auomoto/BOSS-specMech/Software/BasicMicro/2022-05-01 Motion Studio Screen General Settings.PNG

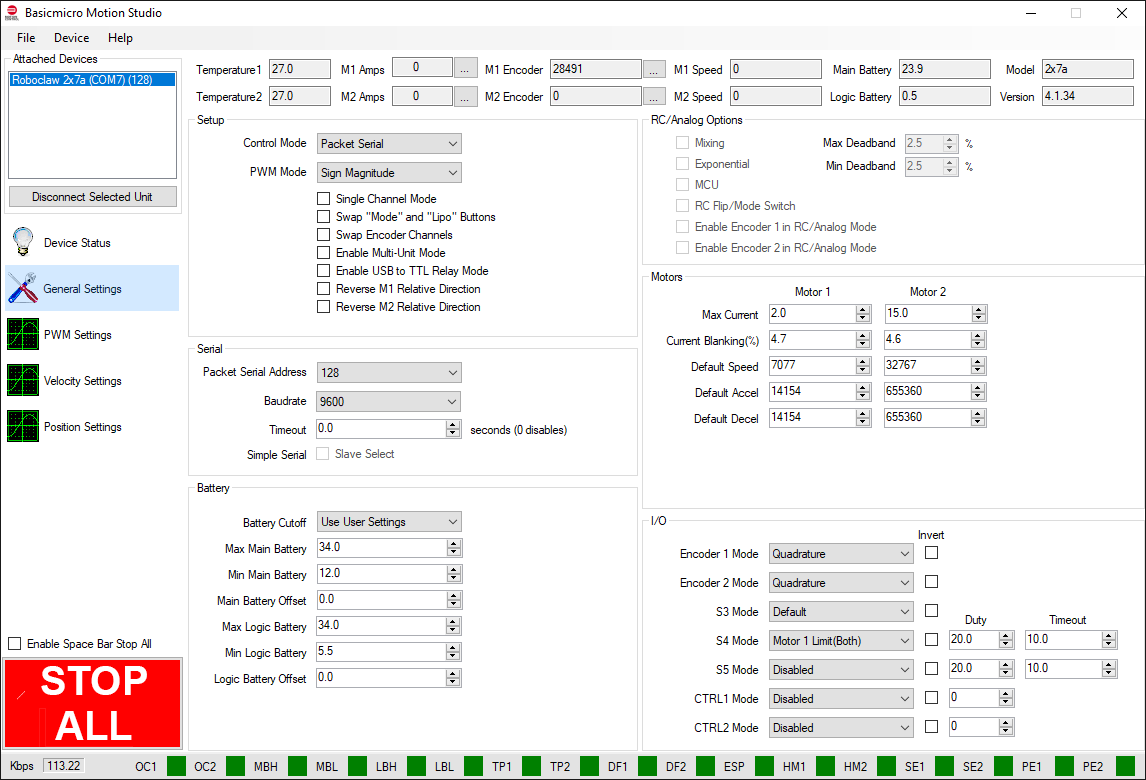
Software/BasicMicro/2022-05-01 Motion Studio Screen General Settings.PNG
