auomoto/BOSS-specMech/Software/Atmel Studio/specMech/roboclaw.c

#include "globals.h"
#include "roboclaw.h"

volatile uint8_t timerSAVEENCODER;
uint8_t timeoutSAVEENCODER, motorDir[3], motorLim[3];
PID pid;

/*------------------------------------------------------------------------------
uint16_t crc16(uint8_t *packet, uint16_t nbytes)

	RoboClaw sends a CRC16 word at the end of data packets and requires a CRC16
	word at the end of commands that send data (not just a command). See page 59
	of the RoboClaw user manual Rev 5.7 (2015) for this routine.

	Inputs:
		packet - array to compute
		nBytes - length of the array

	Returns:
		The CRC16 value, an unsigned 16-bit word
------------------------------------------------------------------------------*/
uint16_t crc16(uint8_t *packet, uint16_t nBytes)
{

	uint8_t bit;
	uint16_t crc = 0;
	int16_t byte;

	for (byte = 0; byte < nBytes; byte++) {
		crc = crc ^ ((uint16_t) packet[byte] << 8);
		for (bit = 0; bit < 8; bit++) {
			if (crc & 0x8000) {
				crc = (crc << 1) ^ 0x1021;
			} else {
				crc = crc << 1;
			}
		}
	}

	return (crc);

}

uint8_t get_FRAM_ENCSAVETIME(char *isotime)
{

	char strbuf[80];
	const char fmt0[] = "get_FRAM_ENCSAVETIME: read_FRAM error";

	if (read_FRAM(FRAMTWIADDR, ENC_SAVETIME, (uint8_t*) isotime, 20) == ERROR) {
		sprintf(strbuf, fmt0);
		printError(ERR_MTR, strbuf);
		return(ERROR);
	}
	isotime[19] = '\0';
	return(NOERROR);

}

/*------------------------------------------------------------------------------
uint8_t get_FRAM_MOTOR_ENCODER(uint8_t controller, uint32_t *encoderValue)

	Retrieves the encoder value stored in FRAM.

	Inputs:
		controller: The controller address: MOTOR_A, MOTOR_B, or MOTOR_C

	Outputs:
		encoderValue: The stored encoder value

	Returns:
		ERROR on FRAM read error
		NOERROR otherwise
------------------------------------------------------------------------------*/
uint8_t get_FRAM_MOTOR_ENCODER(uint8_t controller, int32_t *encoderValue)
{

	char strbuf[80];
	uint8_t tbuf[4];
	uint16_t framaddr;
	const char fmt0[] ="get_FRAM_MOTOR_ENCODER: read_FRAM error for %c";

	switch (controller) {

		case MOTOR_A:
			framaddr = ENCA_FRAMADDR;
			break;

		case MOTOR_B:
			framaddr = ENCB_FRAMADDR;
			break;

		case MOTOR_C:
			framaddr = ENCC_FRAMADDR;
			break;

		default:
			return(ERROR);

	}

	if (read_FRAM(FRAMTWIADDR, framaddr, tbuf, 4) == ERROR) {
		sprintf(strbuf, fmt0, (char) (controller-63));
		printError(ERR_FRAM, strbuf);
		*encoderValue = BADLONG;
		return(ERROR);
	}

	*encoderValue =  (uint32_t) tbuf[0] << 24;
	*encoderValue |= (uint32_t) tbuf[1] << 16;
	*encoderValue |= (uint32_t) tbuf[2] << 8;
	*encoderValue |= (uint32_t) tbuf[3];

	return(NOERROR);

}

/*------------------------------------------------------------------------------
uint8_t get_MOTOR(uint8_t mtraddr, uint8_t cmd, uint8_t* data, uint8_t nbytes)

	Retrieves raw data from the motor controller "mtraddr"

	Inputs:
		mtraddr:	MOTOR_A, MOTOR_B, or MOTOR_C (128, 129, or 130)
		command:	The motor controller packet serial command
		nbytes:		Number of bytes expected from the motor controller,
					not including the two CRC bytes.

	Output:
		data:		Array to receive the data. Undefined if ERROR returned.

	Returns
		ERROR on USART timeout or CRC mismatch
		NOERROR otherwise
------------------------------------------------------------------------------*/
uint8_t get_MOTOR(uint8_t mtraddr, uint8_t cmd, uint8_t* data, uint8_t nbytes)
{

	char strbuf[80];
	uint8_t i, nbytesp2, tbuf[nbytes+2];
	uint16_t crc, crcReceived, crcExpected;
	const char fmt0[] = "get_MOTOR: serial timeout on %c";
	const char fmt1[] = "get_MOTOR: CRC mismatch on %c";

	nbytesp2 = nbytes + 2;
	ser_recv1.nxfrd = 0;			// Set up receive buffer
	ser_recv1.n2xfr = nbytesp2;		// Data plus 2 bytes CRC

	tbuf[0] = mtraddr;				// Motor controller serial address
	tbuf[1] = cmd;					// Motor controller command
	crc = crc16(tbuf, 2);
	tbuf[2] = (crc >> 8) & 0xFF;
	tbuf[3] = crc & 0xFF;

#ifdef VERBOSE
	sprintf(strbuf, " addr=%d cmd=%d crc=0x%04X n2xfr=%d",
		mtraddr, cmd, crc, nbytesp2);
	printLine(strbuf);
#endif

	send_USART1(tbuf, 2);

	USART1_ticks = 0;
	while (ser_recv1.nxfrd < ser_recv1.n2xfr) {
		if (USART1_ticks > 100) {		// Check the number
			sprintf(strbuf, fmt0, (char) (mtraddr-63));
			printError(ERR_MTRREADENC, strbuf);

#ifdef VERBOSE
			break;
#endif
			return(ERROR);
		}
	}

#ifdef VERBOSE
	sprintf(strbuf, " get_MOTOR: USART1_ticks=%d nxfrd=%d", USART1_ticks, ser_recv1.nxfrd);
	printLine(strbuf);
	for (i = 0; i < ser_recv1.nxfrd; i++) {
		sprintf(strbuf, " n=%d %d (0x%02X)", i, ser_recv1.data[i], ser_recv1.data[i]);
		printLine(strbuf);
	}
#endif

	crcReceived = (ser_recv1.data[nbytes] << 8) | ser_recv1.data[nbytes+1];

	for (i = 2; i < nbytesp2; i++) {		// Compute expected crc value
		tbuf[i] = ser_recv1.data[i-2];
	}
	crcExpected = crc16(tbuf, nbytesp2);

	if (crcReceived != crcExpected) {
		sprintf(strbuf, fmt1, (char) (mtraddr-63));
		printError(ERR_MTRENCCRC, strbuf);
		return(ERROR);
	}

	for (i = 0; i < nbytes; i++) {
		data[i] = ser_recv1.data[i];
	}

	return(NOERROR);	

}

/*------------------------------------------------------------------------------
uint8_t get_MOTOR_CURRENT(uint8_t mtraddr, int16_t *current)

	Retrieves motor current in mA from mtraddr

	Inputs:
		mtraddr: MOTOR_A, MOTOR_B, or MOTOR_C (128, 129, or 130)

	Output:
		current: The current in mA

	Returns
		ERROR on USART timeout
		NOERROR otherwise

	This command returns the current for both motor 1 and motor 2. We only
	have a motor 1 so we discard the 2nd value.
------------------------------------------------------------------------------*/
uint8_t get_MOTOR_CURRENT(uint8_t mtraddr, uint16_t *current)
{

	const char fmt0[] = "get_MOTOR_CURRENT: get_MOTOR error on %c";
	char strbuf[80];
	uint8_t data[4];

	if (get_MOTOR(mtraddr, READCURRENT, data, 4) == ERROR) {
		sprintf(strbuf, fmt0, (char) (mtraddr-63));
		printError(ERR_MTR, strbuf);
		*current = BADINT;
		return(ERROR);
	}

	*current = (((uint16_t) data[0] << 8) | (uint16_t) data[1]) * 10;

	return(NOERROR);

}

/*------------------------------------------------------------------------------
uint8_t get_MOTOR_ENCODER(uint8_t mtraddr, int32_t *encoderValue)

	Retrieves the 32-bit encoder value from the controller at mtraddr

	Inputs:
		mtraddr: MOTOR_A, MOTOR_B, or MOTOR_C (128, 129, or 130)

	Output:
		encoderValue: The raw encoder value

	Returns
		ERROR on USART timeout
		NOERROR otherwise

	Also available with this command but not output here:
		status - from page 86 of version 5.7 of the manual:
			Bit0: Counter underflow (1=underflow occurred, clear after reading)
			Bit1: Direction (0=forward, 1-backwards)
			Bit2: Counter overflow (1=overflow occurred, clear after reading)
			Bits 3-7 are "reserved." Bit7 is 1.
------------------------------------------------------------------------------*/
uint8_t get_MOTOR_ENCODER(uint8_t mtraddr, int32_t *encoderValue)
{

	char strbuf[80];
	uint8_t data[5];	// 5 bytes includes status, which is ignored here
	const char fmt0[] = "get_MOTOR_ENCODER: get_MOTOR error on %c";

	if (get_MOTOR(mtraddr, ENCODERCOUNT, data, 5) == ERROR) {
		sprintf(strbuf, fmt0, (char) (mtraddr-63));
		printError(ERR_MTR, strbuf);
		return(ERROR);
	}

	*encoderValue =  (uint32_t) data[0] << 24;
	*encoderValue |= (uint32_t) data[1] << 16;
	*encoderValue |= (uint32_t) data[2] << 8;
	*encoderValue |= (uint32_t) data[3];

#ifdef VERBOSE
	sprintf(strbuf, " encval=%ld", *encoderValue);
	printLine(strbuf);
#endif

	return(NOERROR);

}

/*------------------------------------------------------------------------------
uint8_t get_MOTOR_FLOAT(uint8_t mtraddr, uint8_t cmd, float *value)

	Retrieves a floating point value (the voltage or temperature) from a
	RoboClaw controller.

	Inputs:
		mtraddr:	Controller address (128, 129, 130)
		cmd:		READMAINVOLTAGE (command 24) or
					READTEMPERATURE (command 82)

	Outputs:
		value:		The integer value from the command in increments of tenths of
					a volt or tenths of a degree. The value returned is divided by 10
					to present units of degrees C and volts.

	Returns:
		ERROR on a bad get_MOTOR call
		NOERROR otherwise
------------------------------------------------------------------------------*/
uint8_t get_MOTOR_FLOAT(uint8_t mtraddr, uint8_t cmd, float* value)
{

	char strbuf[80];
	uint8_t data[2];
	const char fmt0[] = "get_MOTOR_FLOAT: get_MOTOR error on %c";

	if (get_MOTOR(mtraddr, cmd, data, 2) == ERROR) {
		sprintf(strbuf, fmt0, (char) (mtraddr-63));
		printError(ERR_MTR, strbuf);
		*value = BADFLOAT;
		return(ERROR);
	}

	*value = ((float) ((data[0] << 8) | data[1])) / 10.0;

	return(NOERROR);

}

uint8_t get_MOTOR_LIMIT(uint8_t mtraddr)
{

	char strbuf[80];
	const char fmt0[] = "get_MOTOR_LIMIT: get_MOTOR_STATUS error on %c";
	uint32_t robostatus;

	if (get_MOTOR_STATUS(mtraddr, &robostatus) == ERROR) {
		sprintf(strbuf, fmt0, (char) (mtraddr - 31));
		printError(ERR_MTR, strbuf);
	}

	if (robostatus & 0x400000) {
		return(YES);
	} else {
		return(NO);
	}

}


/*------------------------------------------------------------------------------
uint8_t get_MOTOR_LIMITS(void)

	Finds the limit switch stored state for every motor.

	Input:
		None

	Output:
		motorLim[n] limit switch states YES, NO, or MTRLIMUNKNOWN

	Returns:
		ERROR on get_MOTOR_STATUS error (quietly)
		NOERROR otherwise

	Note: This does not read the limit switch directly. When the limit switch
		is triggered the switch state is saved but the state is cleared
		immediately after a motor motion in the opposite direction, even
		though the switch itself might still be engaged.
------------------------------------------------------------------------------*/
uint8_t get_MOTOR_LIMITS(void)
{

	uint8_t i, mtraddr;
	uint32_t robostatus;

	for (i = 0; i < 3; i++) {
		motorLim[i] = MTRLIMUNKNOWN;
		mtraddr = i + MOTOR_A;
		if (get_MOTOR_STATUS(mtraddr, &robostatus) != ERROR) {
			if (robostatus & 0x400000) {
				motorLim[i] = YES;
			}
		}
	}

	return(NOERROR);

}

/*------------------------------------------------------------------------------
uint8_t get_MOTOR_MAXCURRENT(uint8_t mtraddr, int32_t *maxCurrent)

	Read the maximum current allowed by the controller.

	Input:
		mtraddr:	MOTOR_A, MOTOR_B, or MOTOR_C (128, 129, 130)

	Output:
		maxCurrent:	The maximum current allowed, in mA

	Returns:
		ERROR on get_MOTOR error
		NOERROR otherwise
------------------------------------------------------------------------------*/
uint8_t get_MOTOR_MAXCURRENT(uint8_t mtraddr, int32_t *maxCurrent)
{

	const char fmt0[] = "get_MOTOR_MAXCURRENT: get_MOTOR error on %c";
	char strbuf[80];
	uint8_t data[8];

	if (get_MOTOR(mtraddr, GETMAXCURRENT, data, 8) == ERROR) {
		sprintf(strbuf, fmt0, (char) (mtraddr-63));
		printError(ERR_MTR, strbuf);
		return(ERROR);
	}

	*maxCurrent =  (uint32_t) data[0] << 24;
	*maxCurrent |= (uint32_t) data[1] << 16;
	*maxCurrent |= (uint32_t) data[2] << 8;
	*maxCurrent |= (uint32_t) data[3];
	*maxCurrent *= 10;	// Convert to mA

	return(NOERROR);

}

/*------------------------------------------------------------------------------
uint8_t get_MOTOR_PID(uint8_t mtraddr, PID *pid)

	Retrieves the PID, maxI, deadZone, minPos, and maxPos from mtraddr

	Inputs:
		mtraddr: The motor controller address(MOTOR_A, MOTOR_B, or MOTOR_C)

	Outputs:
		pid: The stored parameters in the controller

	Returns:
		ERROR on get_MOTOR fail
		NOERROR otherwise
------------------------------------------------------------------------------*/
uint8_t get_MOTOR_PID(uint8_t mtraddr, PID *pid)
{

	const char fmt0[] = "get_MOTOR_PID: get_MOTOR error on %c";
	char strbuf[80];
	uint8_t data[28];
	int32_t p, i, d, maxI, deadZone, minPos, maxPos, qpps;

	if (get_MOTOR(mtraddr, READPID, data, 28) == ERROR) {
		sprintf(strbuf, fmt0, (char) (mtraddr-63));
		printError(ERR_MTR, strbuf);
		return(ERROR);
	}

	p =  (uint32_t) data[0] << 24;
	p |= (uint32_t) data[1] << 16;
	p |= (uint32_t) data[2] << 8;
	p |= (uint32_t) data[3];
	pid->p = (float) p / 1024.0;

	i =  (uint32_t) data[4] << 24;
	i |= (uint32_t) data[5] << 16;
	i |= (uint32_t) data[6] << 8;
	i |= (uint32_t) data[7];
	pid->i = (float) i / 1024.0;

	d =  (uint32_t) data[8] << 24;
	d |= (uint32_t) data[9] << 16;
	d |= (uint32_t) data[10] << 8;
	d |= (uint32_t) data[11];
	pid->d = (float) d / 1024.0;

	maxI =  (uint32_t) data[12] << 24;
	maxI |= (uint32_t) data[13] << 16;
	maxI |= (uint32_t) data[14] << 8;
	maxI |= (uint32_t) data[15];
	pid->maxI = maxI;

	deadZone =  (uint32_t) data[16] << 24;
	deadZone |= (uint32_t) data[17] << 16;
	deadZone |= (uint32_t) data[18] << 8;
	deadZone |= (uint32_t) data[19];
	pid->deadZone = deadZone;

	minPos =  (uint32_t) data[20] << 24;
	minPos |= (uint32_t) data[21] << 16;
	minPos |= (uint32_t) data[22] << 8;
	minPos |= (uint32_t) data[23];
	pid->minPos = minPos;

	maxPos =  (uint32_t) data[24] << 24;
	maxPos |= (uint32_t) data[25] << 16;
	maxPos |= (uint32_t) data[26] << 8;
	maxPos |= (uint32_t) data[27];
	pid->maxPos = maxPos;

	if (get_MOTOR(mtraddr, READQPPS, data, 16) == ERROR) {
		sprintf(strbuf, fmt0, (char) (mtraddr-63));
		printError(ERR_MTR, strbuf);
		return(ERROR);
	}

	qpps = (uint32_t) data[12] << 24;
	qpps |= (uint32_t) data[13] << 16;
	qpps |= (uint32_t) data[14] << 8;
	qpps |= (uint32_t) data[15];
	pid->qpps = qpps;

	return(NOERROR);

}

/*------------------------------------------------------------------------------
uint8_t get_MOTOR_S4MODE(uint8_t mtraddr, uint8_t *mode)

	Retrieve the S4 input pin behavior. The S4 pin is connected to both the
	forward and rearward limit switches. We want to see 0x42 mode, which means
	the S4 pin treats sees a home switch when moving backwards and a limit
	switch when moving forward. When encountering the home switch, the 2x7A
	controller resets the encoder value to 0 (actually, something close).

	Inputs:
		mtraddr:	The controller serial address

	Outputs:
		*mode:		The retrieved mode for the S4 pin (should be 0x72)

	Returns:
		ERROR if the get_MOTOR routine fails
		NOERROR otherwise

	Note: One of the modes, Motor 1 Limit(Both) returns 0x02 when it should
		return 0x32
------------------------------------------------------------------------------*/
uint8_t get_MOTOR_S4MODE(uint8_t mtraddr, uint8_t *mode)
{

	const char fmt0[] = "get_MOTOR_S4: get_MOTOR error on %c";
	char strbuf[80];
	uint8_t data[3];

	if (get_MOTOR(mtraddr, GETS4MODE, data, 3) == ERROR) {
		sprintf(strbuf, fmt0, (char) (mtraddr-63));
		printError(ERR_MTR, strbuf);
		*mode = 0xFF; 
		return(ERROR);
	}

	*mode = data[1];

	return(NOERROR);

}

/*------------------------------------------------------------------------------
uint8_t get_MOTOR_SPEED(uint8_t mtraddr, int32_t *speed)

	Retrieves the motor speed from the controller at mtraddr

	Inputs:
		mtraddr:	MOTOR_A, MOTOR_B, or MOTOR_C (128, 129, or 130)

	Output:
		speed:		The speed in encoder counts/sec. 2-s complement value.

	Returns
		ERROR on USART timeout
		NOERROR otherwise

	Also available with this command but not output here:
		status - from page 86 of version 5.7 of the manual:
			Bit0: Counter underflow (1=underflow occurred, clear after reading)
			Bit1: Direction (0=forward, 1-backwards)
			Bit2: Counter overflow (1=overflow occurred, clear after reading)
			Bits 3-7 are "reserved." Bit7 is 1.
------------------------------------------------------------------------------*/
uint8_t get_MOTOR_SPEED(uint8_t mtraddr, int32_t *speed)
{

	char strbuf[80];
	uint8_t data[5];
	const char fmt0[] = "get_MOTOR_SPEED: get_MOTOR call error on %c";

	if (get_MOTOR(mtraddr, ENCODERSPEED, data, 5) == ERROR) {
		sprintf(strbuf, fmt0, (char) (mtraddr-63));
		printError(ERR_MTR, strbuf);
		return(ERROR);
	}

	*speed =  (uint32_t) data[0] << 24;
	*speed |= (uint32_t) data[1] << 16;
	*speed |= (uint32_t) data[2] << 8;
	*speed |= (uint32_t) data[3];

	return(NOERROR);

}

/*------------------------------------------------------------------------------
uint8_t get_MOTOR_STATUS(uint8_t mtraddr, uint32_t *robostatus)

	Reads the motor controller status. Command 90, see page 73 of the RoboClaw
	User Manual, Revision 5.7. We use this to determine if a limit switch has
	been triggered (the S4 pin is pulled low). The bitmask for S4 is 0x400000.

	Input:
		Motor address (128, 129, or 130).

	Output:
		The 32-bit word in robostatus.

	Returns:
		ERROR if the get_MOTOR command fails.

------------------------------------------------------------------------------*/
uint8_t get_MOTOR_STATUS(uint8_t mtraddr, uint32_t *robostatus)
{
	
	char strbuf[80];
	const char fmt0[] = "get_MOTOR_STATUS: get_MOTOR error %c";
	uint8_t data[4];

	if (get_MOTOR(mtraddr, ROBOSTATUS, data, 4) == ERROR) {
		sprintf(strbuf, fmt0, (char) mtraddr-63);
		printError(ERR_MTR, strbuf);
		return(ERROR);
	}

	*robostatus =  (uint32_t) data[0] << 24;
	*robostatus |= (uint32_t) data[1] << 16;
	*robostatus |= (uint32_t) data[2] << 8;
	*robostatus |= (uint32_t) data[3];

	return(NOERROR);

}

/*------------------------------------------------------------------------------
uint8_t init_MOTORS(void)
	Reads the last-saved encoder values from FRAM and loads them into the three
	controllers.

	Inputs: None

	Outputs: None

	Returns
		ERROR if put_MOTOR_ENCODER fails
		NOERROR otherwise

ADD ERROR CHECKS?
------------------------------------------------------------------------------*/
uint8_t init_MOTORS(void)
{

	uint8_t i, mtraddr;
	int32_t encoderValue;

	_delay_ms(100);		// Wait to boot up
	timerSAVEENCODER = 0;
	timeoutSAVEENCODER = SAVEENCODERPERIOD;

	for (i = 0; i < NMOTORS; i++) {
		motorDir[i] = MTRDIRUNKNOWN;
		motorLim[i] = MTRLIMUNKNOWN;
		mtraddr = i + MOTOR_A;
		get_FRAM_MOTOR_ENCODER(mtraddr, &encoderValue);
		put_MOTOR_ENCODER(mtraddr, encoderValue);
	}

	return(NOERROR);

}

/*------------------------------------------------------------------------------
uint8_t motorMoving(uint8_t mtraddr)

	Checks encoder speed to see if the motor is moving

	Input:
		mtraddr: The controller address

	Output:
		None

	Returns:
		YES if the motor is moving
		NO if it isn't
------------------------------------------------------------------------------*/
uint8_t motorMoving(uint8_t mtraddr)
{

	const char fmt0[] = "motorMoving: get_MOTOR_SPEED error on %c";
	char strbuf[80];
	int32_t encoderSpeed;

	encoderSpeed = 0;
	if (get_MOTOR_SPEED(mtraddr, &encoderSpeed) == ERROR) {
		sprintf(strbuf, fmt0, (char) (mtraddr-63));
		printError(ERR_MTR, strbuf);
		return(ERROR);
	}

	if (encoderSpeed != 0) {
		return(YES);
	} else {
		return(NO);
	}

}

/*------------------------------------------------------------------------------
uint8_t motorsMoving(void)
	Returns YES if any motors are moving. Emits an error message if a
	controller does not respond, but does not return "ERROR"
------------------------------------------------------------------------------*/
uint8_t motorsMoving(void)
{

	const char fmt1[] = "motorsMoving: get_MOTOR_SPEED error on %c";
	char strbuf[80];
	uint8_t i, mtraddr, nmoving;
	int32_t encoderSpeed;

	encoderSpeed = 0;
	nmoving = 0;

	for (i = 0; i < NMOTORS; i++) {
		mtraddr = i + MOTOR_A;
		if (get_MOTOR_SPEED(mtraddr, &encoderSpeed) == ERROR) {
			sprintf(strbuf, fmt1, (char) (mtraddr-63));
			printError(ERR_MTR, strbuf);
			continue;
		}
		if (encoderSpeed != 0) {
			nmoving++;
		}
	}

	if (nmoving) {
		return(YES);
	} else {
		return(NO);
	}

}

/*------------------------------------------------------------------------------
uint8_t move_MOTOR(uint8_t mtraddr, int32_t newPosition)
	Move to newPosition (encoder units).

	Input:
		mtraddr:		MOTOR_A, MOTOR_B, or MOTOR_C
		newPosition:	The target encoder value

	Returns:
		ERROR if an unknown motor designator
		NOERROR otherwise
------------------------------------------------------------------------------*/
uint8_t move_MOTOR(uint8_t mtraddr, int32_t newPosition)
{

	const char fmt1[] = "move_MOTOR: put_MOTOR error on %c";
	char strbuf[80];
	uint8_t buffer, data[17], nbytes, mtrIndex;
	uint32_t acceleration, deceleration, speed;
	int32_t oldPosition;

	nbytes = 17;
	buffer = 1;
	acceleration = ACCELERATION;	// See roboclaw.h
	deceleration = DECELERATION;
	speed = SPEED;
	mtrIndex = mtraddr - MOTOR_A;

	get_MOTOR_ENCODER(mtraddr, &oldPosition);

	if (newPosition == oldPosition) {
		return(NOERROR);
	}

	data[0] = (acceleration >> 24) & 0XFF;
	data[1] = (acceleration >> 16) & 0xFF;
	data[2] = (acceleration >> 8) & 0xFF;
	data[3] = (acceleration) & 0xFF;
	data[4] = (speed >> 24) & 0xFF;
	data[5] = (speed >> 16) & 0xFF;
	data[6] = (speed >> 8) & 0xFF;
	data[7] = (speed) & 0xFF;
	data[8] = (deceleration >> 24) & 0xFF;
	data[9] = (deceleration >> 16) & 0xFF;
	data[10] = (deceleration >> 8) & 0xFF;
	data[11] = (deceleration) & 0xFF;
	data[12] = (newPosition >> 24) & 0xFF;
	data[13] = (newPosition >> 16) & 0xFF;
	data[14] = (newPosition >> 8) & 0xFF;
	data[15] = (newPosition) & 0xFF;
	data[16] = buffer;

#ifdef VERBOSE
	sprintf(strbuf, " move_MOTOR to newpos=%ld", newPosition);
	printLine(strbuf);
#endif

	if (newPosition > oldPosition) {
		motorDir[mtrIndex] = MTRDIRPOSITIVE;
	} else if (newPosition < oldPosition) {
		motorDir[mtrIndex] = MTRDIRNEGATIVE;
	}

	if (put_MOTOR(mtraddr, DRIVETO, data, nbytes) == ERROR) {
		motorDir[mtrIndex] = MTRDIRUNKNOWN;
		sprintf(strbuf, fmt1, (char) (mtraddr-63));
		printError(ERR_MTR, strbuf);
		return(ERROR);
	}

	return(NOERROR);

}

/*------------------------------------------------------------------------------
uint8_t move_MOTOR_CMD(uint8_t cstack)
	Interprets the m command and calls for the move

	Input:
		cstack: command stack position

	Returns:
		ERROR if an unknown motor designator (not A, B, C, or a, b, c) is read
		NOERROR otherwise
------------------------------------------------------------------------------*/
uint8_t move_MOTOR_CMD(uint8_t cstack)
{

	char strbuf[80];
	uint8_t motor, controller;
	int32_t newPosition, currentPosition, deltaPos;
	const char fmt0[] = "move_MOTOR_CMD: get_MOTOR_ENCODER error";
	const char fmt1[] = "move_MOTOR_CMD: unknown motor";
	const char fmt2[] = "move_MOTOR_CMD: move_MOTOR error";
	const char fmt3[] = "move_MOTOR_CMD: move_MOTORS_PISTON error";

	if (pcmd[cstack].cvalue[0] == '\0') {	// Don't do anything on null distance
		return(NOERROR);
	}

	motor = pcmd[cstack].cobject;

	switch(motor) {

		case 'A':			// Move absolute
		case 'B':
		case 'C':
			controller = motor + 63;
			if (get_MOTOR_ENCODER(controller, &currentPosition) == ERROR) {
				sprintf(strbuf, fmt0);
				printError(ERR_MTR_ENC_VAL, strbuf);
				return(ERROR);
			}
			newPosition = (atol(pcmd[cstack].cvalue) * ENC_COUNTS_PER_MICRON);
			break;

		case 'a':			// Move relative
		case 'b':
		case 'c':
			controller = motor + 31;
			if (get_MOTOR_ENCODER(controller, &currentPosition) == ERROR) {
				sprintf(strbuf, fmt0);
				printError(ERR_MTR_ENC_VAL, strbuf);
				return(ERROR);
			}
			newPosition = currentPosition + (atol(pcmd[cstack].cvalue) * ENC_COUNTS_PER_MICRON);
			break;

		case 'd':
			deltaPos = (atol(pcmd[cstack].cvalue) * ENC_COUNTS_PER_MICRON);
			if (move_MOTORS_PISTON(deltaPos) == ERROR) {
				sprintf(strbuf, fmt3);
				printError(ERR_MTR, strbuf);
				return(ERROR);
			}
			return(NOERROR);

		default:
			sprintf(strbuf, fmt1);
			printError(ERR_MTR, strbuf);
			return(ERROR);
			break;	
	}

	motorDir[controller - MOTOR_A] = MTRDIRUNKNOWN;

	if (move_MOTOR(controller, newPosition) == ERROR) {
		sprintf(strbuf, fmt2);
		printError(ERR_MTR, strbuf);
		return(ERROR);
	}

	if (newPosition < currentPosition) {
		motorDir[controller - MOTOR_A] = MTRDIRNEGATIVE;
	} else if (newPosition > currentPosition) {
		motorDir[controller - MOTOR_A] = MTRDIRPOSITIVE;
	}

	return(NOERROR);

}

uint8_t move_MOTOR_HOME(void)
{

	const char fmt0[] = "move_MOTOR_HOME: timeout";
	const char fmt1[] = "move_MOTOR_HOME: get_MOTOR_ENCODER error on %c";
	const char fmt2[] = "move_MOTOR_HOME: move_MOTOR error on %c";
	const char fmt3[] = "move_MOTOR_HOME: motors didn't align";
	char strbuf[80];
	uint8_t i, mtraddr;
	int32_t curPos[3], avgPos;

	avgPos = 0;

	for (i = 0; i < 1; i++) {
//	for (i = 0; i < 3; i++) {
		mtraddr = i + MOTOR_A;
		if (get_MOTOR_ENCODER(mtraddr, &curPos[i]) == ERROR) {
			sprintf(strbuf, fmt1, (char) (mtraddr-63));
			printError(ERR_MTR, strbuf);
			return(ERROR);
		}
		avgPos += curPos[i];
	}
	avgPos /= 3;

#ifdef VERBOSE
	sprintf(strbuf, " avgPos = %ld", avgPos/ENC_COUNTS_PER_MICRON);
	printLine(strbuf);
#endif

	for (mtraddr = MOTOR_A; mtraddr <= MOTOR_A; mtraddr++) {
//	for (mtraddr = MOTOR_A; mtraddr <= MOTOR_C; mtraddr++) {
		if (move_MOTOR(mtraddr, avgPos) == ERROR) {
			sprintf(strbuf, fmt2, (char) (mtraddr-63));
			printError(ERR_MTR, strbuf);
			return(ERROR);
		}
	}

	_delay_ms(250);		// give motors a chance to start up

// BREAK UP THIS ROUTINE INTO PIECES CONTROLLED FROM MAIN

	i = 0;
	while (motorsMoving()) {
		if (i > 20) {				// get this number right later
			sprintf(strbuf, fmt0);
			printError(ERR_MTR, strbuf);
			return(ERROR);
		}
		i++;
		_delay_ms(1000);
	}

#ifdef VERBOSE
	sprintf(strbuf, " stopped after %d", i);
	printLine(strbuf);
#endif

	for (i = 0; i < 1; i++) {
//	for (i = 0; i < 4; i++) {
		mtraddr = i + MOTOR_A;
		if (get_MOTOR_ENCODER(mtraddr, &curPos[i]) == ERROR) {
			sprintf(strbuf, fmt1, mtraddr-63);
			printError(ERR_MTR, strbuf);
			return(ERROR);
		}
	}

	// Check that all motors are at the same position
	if (abs( (int)(curPos[0] - curPos[1]) ) > ENC_COUNTS_PER_MICRON) {
		sprintf(strbuf, fmt3);
		printError(ERR_MTR, strbuf);
		return(ERROR);
	}
	if (abs( (int)(curPos[0] - curPos[2]) ) > ENC_COUNTS_PER_MICRON) {
		sprintf(strbuf, fmt3);
		printError(ERR_MTR, strbuf);
		return(ERROR);
	}
	// now piston the motors to somewhere close (200 um in this case)
	for (mtraddr = MOTOR_A; mtraddr <= MOTOR_A; mtraddr++) {
//	for (mtraddr = MOTOR_A; mtraddr <= MOTOR_C; mtraddr++) {
		if (move_MOTOR(mtraddr, (int32_t) (200L * ENC_COUNTS_PER_MICRON)) == ERROR) {
			sprintf(strbuf, fmt2, (char) (mtraddr-63));
			printError(ERR_MTR, strbuf);
			return(ERROR);
		}
	}


/*---------

	// and back into the switch
	for (mtraddr = MOTOR_A; mtraddr <= MOTOR_A; mtraddr++) {
//	for (mtraddr = MOTOR_A; mtraddr <= MOTOR_C; mtraddr++) {
		if (move_MOTOR(mtraddr, -100) == ERROR) {
			sprintf(strbuf, fmt2, (char) (mtraddr-63));
			printError(ERR_MTR, strbuf);
			return(ERROR);
		}
	}

	for (mtraddr = MOTOR_A; mtraddr <= MOTOR_A; mtraddr++) {
//	for (mtraddr = MOTOR_A; mtraddr <= MOTOR_C; mtraddr++) {
		if (put_MOTOR_ENCODER(mtraddr, 0UL) == ERROR) {
			sprintf(strbuf, fmt4, (char) (mtraddr-63));
			printError(ERR_MTR, strbuf);
			return(ERROR);
		}
	}

-------------*/

	return(NOERROR);

}

uint8_t move_MOTORS_PISTON(int32_t deltaValue)
{

	char strbuf[80];
	uint8_t i, mtraddr;
	int32_t curPos[3], newPos[3];
	const char fmt0[] = "move_MOTORS_PISTON: get_MOTOR_ENCODER error on %c";
	const char fmt1[] = "move_MOTORS_PISTON: move_MOTOR error on %c";

	for (i = 0; i < NMOTORS; i++) {
		mtraddr = i + MOTOR_A;
		if (get_MOTOR_ENCODER(mtraddr, &curPos[i]) == ERROR) {
			sprintf(strbuf, fmt0, mtraddr-63);
			printError(ERR_MTR, strbuf);
			return(ERROR);
		}
		newPos[i] = curPos[i] + deltaValue;
	}

	for (i = 0; i < NMOTORS; i++) {
		mtraddr = i + MOTOR_A;
		if (move_MOTOR(mtraddr, newPos[i]) == ERROR) {
			sprintf(strbuf, fmt1, mtraddr-63);
			printError(ERR_MTR, strbuf);
			return(ERROR);
		}
		motorDir[i] = MTRDIRUNKNOWN;
		if (newPos[i] > curPos[i]) {
			motorDir[i] = MTRDIRPOSITIVE;
		} else if (newPos[i] < curPos[i]) {
			motorDir[i] = MTRDIRNEGATIVE;
		}
	}

	return(NOERROR);

}

/*------------------------------------------------------------------------------
uint8_t put_FRAM_ENCODERS(void)

	Store the encoder values in FRAM.

	Inputs:
		None

	Outputs:
		None

	Returns:
		ERROR on get_MOTOREncoder or write_FRAM failure
		NOERROR otherwise

	Note:
		This routine is called asynchronously and should't emit error
		messages.
------------------------------------------------------------------------------*/
uint8_t put_FRAM_ENCODERS(void)
{

	char isotime[20];
	uint8_t i, tbuf[4], mtraddr;
	uint16_t memaddr[3] = {ENCA_FRAMADDR, ENCB_FRAMADDR, ENCC_FRAMADDR};
	int32_t encoderValue;

	for (i = 0; i < NMOTORS; i++) {
		mtraddr = i + MOTOR_A;
		if (get_MOTOR_ENCODER(mtraddr, &encoderValue) == ERROR) {
			return(ERROR);
		}
		tbuf[0] = (encoderValue >> 24) & 0xFF;
		tbuf[1] = (encoderValue >> 16) & 0xFF;
		tbuf[2] = (encoderValue >> 8) & 0xFF;
		tbuf[3] = encoderValue & 0xFF;
		if (write_FRAM(FRAMTWIADDR, memaddr[i], tbuf, 4) == ERROR) {
			return(ERROR);
		}
	}

	get_time(isotime);
	write_FRAM(FRAMTWIADDR, ENC_SAVETIME, (uint8_t*) isotime, 20);

	return(NOERROR);

}

/*------------------------------------------------------------------------------
uint8_t put_MOTOR(uint8_t mtraddr, uint8_t cmd, uint8_t* data, uint8_t nbytes)
	Sends a command to a motor controller. This routine copies data to temporary
	array and adds the two CRC bytes before sending the temporary array to the
	controller.

	Inputs:
		mtraddr:	Motor controller serial address
		cmd:		Motor controller command
		data:		Array containing data to send.
		nbytes:		Number of bytes to send (not including the 2 CRC bytes)

	Outputs:
		Nothing

	Returns:
		ERROR:		If a serial timeout or bad acknowledge is detected
		NOERROR:	Otherwise
------------------------------------------------------------------------------*/
uint8_t put_MOTOR(uint8_t mtraddr, uint8_t cmd, uint8_t* data, uint8_t nbytes)
{

	const char fmt1[] = "put_MOTOR: serial timeout on %c";
	const char fmt2[] = "put_MOTOR: bad ACK on %c, ack=0x%02x";
	char strbuf[80];
	uint8_t i, tbuf[nbytes+4];
	uint16_t crc;

	ser_recv1.nxfrd = 0;				// Set up reply
	ser_recv1.n2xfr = 1;				// Receive only the 0xFF ACK

	tbuf[0] = mtraddr;
	tbuf[1] = cmd;
	for (i = 0; i < nbytes; i++) {
		tbuf[i+2] = data[i];
	}
	crc = crc16(tbuf, nbytes+2);
	tbuf[nbytes+2] = (crc >> 8) & 0xFF;
	tbuf[nbytes+3] = crc & 0xFF;

	send_USART1(tbuf, nbytes+4);		// Send the command

	USART1_ticks = 0;
	while (ser_recv1.nxfrd < ser_recv1.n2xfr) {
		if (USART1_ticks > 100) {
			sprintf(strbuf, fmt1, (char) (mtraddr-63));
			printError(ERR_MTR, strbuf);
			return(ERROR);
		} else {
			asm("nop");
		}
	}

#ifdef VERBOSE
	sprintf(strbuf, " put_MOTOR USART1_ticks=%d", USART1_ticks);
	printLine(strbuf);
#endif

	if (ser_recv1.data[0] != 0xFF) {	// Bad ack
		sprintf(strbuf, fmt2, (char) (mtraddr-31), ser_recv1.data[0]);
		printError(ERR_MTR, strbuf);
		return(ERROR);
	}

	return(NOERROR);
	
}

/*------------------------------------------------------------------------------
uint8_t put_MOTOR_ENCODER(uint8_t mtraddr, int32_t encoderValue)
	Writes a new encoder value to the selected controller.

	Inputs:
		mtraddr:		Motor controller serial address
		encoderValue:	The new encoder value

	Outputs:
		Nothing

	Returns:
		ERROR:		If put_MOTOR returns an error
		NOERROR:	Otherwise
------------------------------------------------------------------------------*/
uint8_t put_MOTOR_ENCODER(uint8_t mtraddr, int32_t encoderValue)
{

	const char fmt1[] = "put_MOTOR_ENCODER: put_MOTOR error on %c";
	char strbuf[80];
	uint8_t data[4];

	data[0] = (encoderValue >> 24) & 0xFF;
	data[1] = (encoderValue >> 16) & 0xFF;
	data[2] = (encoderValue >> 8) & 0xFF;
	data[3] = encoderValue & 0xFF;

	if (put_MOTOR(mtraddr, PUTENCODER, data, 4) == ERROR) {
		sprintf(strbuf, fmt1, (char) (mtraddr-63));
		printError(ERR_MTR, strbuf);
		return(ERROR);
	}

	return(NOERROR);

}

/*------------------------------------------------------------------------------
uint8_t put_MOTOR_MAXCURRENT(uint8_t mtraddr, int32_t maxCurrent)
	Writes the maximum current value to the selected controller. This works even
	though the Basic Micro GUI doesn't reflect the change. Reading the device on
	the GUI also doesn't update the number. Writing the settings from the GUI
	*will* write the values to the controller EPROM.

	Inputs:
		mtraddr:		Motor controller serial address
		maxCurrent:		The maximum current value im mA

	Outputs:
		Nothing

	Returns:
		ERROR:			If put_MOTOR returns an error
		NOERROR:		Otherwise
------------------------------------------------------------------------------*/
/*
uint8_t put_MOTOR_MAXCURRENT(uint8_t mtraddr, int32_t maxCurrent)
{

	const char fmt1[] = "put_MOTOR_MAXCURRENT: put_MOTOR error on %c";
	char strbuf[80];
	uint8_t data[8];

	maxCurrent /= 10;			// convert to 10 mA units
	data[0] = (maxCurrent >> 24) & 0xFF;
	data[1] = (maxCurrent >> 16) & 0xFF;
	data[2] = (maxCurrent >> 8) & 0xFF;
	data[3] = maxCurrent & 0xFF;
	data[4] = data[5] = data[6] = data[7] = 0;
	if (put_MOTOR(mtraddr, PUTMAXCURRENT, data, 8) == ERROR) {
		sprintf(strbuf, fmt1, (char) (mtraddr-63));
		printError(ERR_MTR, strbuf);
		return(ERROR);
	}
	return(NOERROR);
}
*/

/*------------------------------------------------------------------------------
uint8_t put_MOTOR_PID(uint8_t mtraddr, PID pid)
	Writes new PID parameters to the selected controller. Besides P, I, and D,
	the PID structure also contains the maximum integral windup (maxI), deadZone,
	and the minimum and maximum allowable encoder values (minPos and maxPos).

	Inputs:
		mtraddr:	Motor controller serial address
		PID:		The new PID values

	Outputs:
		Nothing

	Returns:
		ERROR:		If put_MOTOR returns an error
		NOERROR:	Otherwise
------------------------------------------------------------------------------*/

uint8_t put_MOTOR_PID(uint8_t mtraddr, PID pid)
{

	const char fmt1[] = "put_MOTOR_PID: put_MOTOR error pid on %c";
	const char fmt2[] = "put_MOTOR_PID: put_MOTOR error qpps on %c";
	char strbuf[80];
	uint8_t data[28];
	int32_t p, i, d;

	p = (int32_t) (pid.p * 1024.0);
	i = (int32_t) (pid.i * 1024.0);
	d = (int32_t) (pid.d * 1024.0);

	data[0] = (d >> 24) & 0xFF;
	data[1] = (d >> 16) & 0xFF;
	data[2] = (d >> 8) & 0xFF;
	data[3] = d & 0xFF;
	data[4] = (p >> 24) & 0xFF;
	data[5] = (p >> 16) & 0xFF;
	data[6] = (p >> 8) & 0xFF;
	data[7] = p & 0xFF;
	data[8] = (i >> 24) & 0xFF;
	data[9] = (i >> 16) & 0xFF;
	data[10] = (i >> 8) & 0xFF;
	data[11] = i & 0xFF;
	data[12] = (pid.maxI >> 24) & 0xFF;
	data[13] = (pid.maxI >> 16) & 0xFF;
	data[14] = (pid.maxI >> 8) & 0xFF;
	data[15] = pid.maxI & 0xFF;
	data[16] = (pid.deadZone >> 24) & 0xFF;
	data[17] = (pid.deadZone >> 16) & 0xFF;
	data[18] = (pid.deadZone >> 8) & 0xFF;
	data[19] = pid.deadZone & 0xFF;
	data[20] = (pid.minPos >> 24) & 0xFF;
	data[21] = (pid.minPos >> 16) & 0xFF;
	data[22] = (pid.minPos >> 8) & 0xFF;
	data[23] = pid.minPos & 0xFF;
	data[24] = (pid.maxPos >> 24) & 0xFF;
	data[25] = (pid.maxPos >> 16) & 0xFF;
	data[26] = (pid.maxPos >> 8) & 0xFF;
	data[27] = pid.maxPos & 0xFF;

	if (put_MOTOR(mtraddr, SETPID, data, 28) == ERROR) {
		sprintf(strbuf, fmt1, (char) (mtraddr-63));
		printError(ERR_MTR, strbuf);
		return(ERROR);
	}

	data[0] = data[1] = data[2] = data[3] = 0;
	data[4] = data[5] = data[6] = data[7] = 0;
	data[8] = data[9] = data[10] = data[11] = 0;
	data[12] = (pid.qpps >> 24) & 0xFF;
	data[13] = (pid.qpps >> 16) & 0xFF;
	data[14] = (pid.qpps >> 8) & 0xFF;
	data[15] = pid.qpps & 0xFF;

	if (put_MOTOR(mtraddr, SETQPPS, data, 16) == ERROR) {
		sprintf(strbuf, fmt2, (char) (mtraddr-63));
		printError(ERR_MTR, strbuf);
		return(ERROR);
	}

	return(NOERROR);
}


/*------------------------------------------------------------------------------
uint8_t put_MOTOR_S4MODE(uint8_t mtraddr)
	Writes the S4 input pin behavior. The S4 pin is connected to both the
	forward and rearward limit switches. We write 0x72, which means the S4 pin
	treats one switch as the home position and the other as a limit.

	Inputs:
		mtraddr:	The controller serial address

	Outputs:
		None

	Returns:
		ERROR if the put_MOTOR routine fails
		NOERROR otherwise
------------------------------------------------------------------------------*/
/*
uint8_t put_MOTOR_S4MODE(uint8_t mtraddr, uint8_t s4mode)
{

	char strbuf[80];
	uint8_t data[3];
	const char fmt0[] = "put_MOTOR_S4MODE: put_MOTOR error on %c";

	data[0] = 0x00;
	data[1] = s4mode;
	data[2] = 0x00;

	if (put_MOTOR(mtraddr, SETS4MODE, data, 3) == ERROR) {
		sprintf(strbuf, fmt0, (char) (mtraddr-63));
		printError(ERR_MTR, strbuf);
		return(ERROR);
	}

	return(NOERROR);

}
*/
/*
uint8_t set_MOTOR_PARAMS(void)
{

	char strbuf[80];
	uint8_t mtraddr;
	PID pid;
	const char fmt0[] = "set_MOTOR_PARAMS: put_MOTOR_MAXCURRENT error on %c";
	const char fmt1[] = "set_MOTOR_PARAMS: put_MOTOR_PID error on %c";
	const char fmt2[] = "set_MOTOR_PARAMS: put_MOTOR_S4MODE error on %c";

	pid.p = PID_P;
	pid.i = PID_I;
	pid.d = PID_D;
	pid.maxI = PID_MAXI;
	pid.deadZone = PID_DEADZONE;
	pid.minPos = PID_MINPOS;
	pid.maxPos = PID_MAXPOS;
	pid.qpps = PID_QPPS;

	for (mtraddr = MOTOR_A; mtraddr <= MOTOR_C; mtraddr++) {
		_delay_ms(12);
		if (put_MOTOR_MAXCURRENT(mtraddr, MAXCURRENT) == ERROR) {
			sprintf(strbuf, fmt0, (char) (mtraddr-63));
			printError(ERR_MTR, strbuf);
			return(ERROR);
		}
		_delay_ms(12);
		if (put_MOTOR_PID(mtraddr, pid) == ERROR) {
			sprintf(strbuf, fmt1, (char) (mtraddr-63));
			printError(ERR_MTR, strbuf);
			return(ERROR);
		}
		_delay_ms(12);
		if (put_MOTOR_S4MODE(mtraddr, S4MODE) == ERROR) {
			sprintf(strbuf, fmt2, (char) (mtraddr-63));
			printError(ERR_MTR, strbuf);
			return(ERROR);
		}
	}

	return(NOERROR);

}
*/
/*------------------------------------------------------------------------------
uint8_t stop_MOTOR(uint8_t mtraddr)
	Immediately stop a motor by sending a command 0.

	Inputs:
		mtraddr - Motor controller address (MOTOR_A, MOTOR_B, MOTOR_C)

	Outputs:
		None

	Returns:
		ERROR if the put_MOTOR command fails
------------------------------------------------------------------------------*/
/*
uint8_t stop_MOTOR(uint8_t mtraddr)
{

	char strbuf[80];
	uint8_t tbuf[1];
	const char fmt[] = "stop_MOTOR: put_MOTOR error on %c";

	tbuf[0] = 0;
	if (put_MOTOR(mtraddr, STOP, tbuf, 1) == ERROR) {
		sprintf(strbuf, fmt, (char) (mtraddr-63));
		printError(ERR_MTR, strbuf);
		return(ERROR);
	}

	return(NOERROR);

}
*/
/*------------------------------------------------------------------------------
uint8_t stop_MOTORS(void)
	Immediately stops all motors

	Inputs:
		None

	Outputs:
		None

	Returns:
		ERROR if the stop_MOTOR command fails
------------------------------------------------------------------------------*/
/*
uint8_t stop_MOTORS(void)
{

	char strbuf[80];
	uint8_t i, data[9], mtraddr, errflag;
	const char fmt[] = "stop_MOTORS: put_MOTOR error on %c";

	errflag = 0;
	for (i = 0; i < 8; i++) {
		data[i] = 0;
	}
	data[8] = 1;		// Buffer flag
	for (i = 0; i < NMOTORS; i++) {
		mtraddr = i + MOTOR_A;
		if (put_MOTOR(mtraddr, STOP, data, 9) == ERROR) {
			sprintf(strbuf, fmt, (char) (mtraddr - 63));
			printError(ERR_MTR, strbuf);
			errflag++;
		}
	}

	if (errflag) {
		return(ERROR);
	} else {
		return(NOERROR);
	}

}
*/

/*------------------------------------------------------------------------------
uint8_t unstick_MOTOR_LIMIT(uint8_t cstack)
	Recover from a limit switch hit

	Input:
		cstack

	Output:
		None

	Returns:
		ERROR
		NOERROR
------------------------------------------------------------------------------*/
uint8_t unstick_MOTOR_LIMIT(uint8_t cstack)
{

	char strbuf[80];
	uint8_t i, mtraddr, mtrIndex, direction, stuck;
	int32_t encodervalue, encoderspeed, newPosition;

	mtraddr = pcmd[cstack].cobject + 31;	// 128, 129, or 130
	mtrIndex = mtraddr - MOTOR_A;
	direction = motorDir[mtrIndex];		// Save the most recent command direction

//sprintf(strbuf, "mtraddr = %d, mtrIndex = %d, direction = %d", mtraddr, mtrIndex, direction);
//printLine(strbuf);

	if (get_MOTOR_LIMIT(mtraddr) == NO) {
		sprintf(strbuf, "motor %c not stuck", mtraddr - 31);
		printError(ERR_MTR, strbuf);
		return(NOERROR);
	}

	stuck = YES;
	get_MOTOR_ENCODER(mtraddr, &encodervalue);

//sprintf(strbuf, "current position = %ld", encodervalue);
//printLine(strbuf);

	for (i = 0; i < 3; i++) {

		// Try the opposite direction first
		if (direction == MTRDIRNEGATIVE) {
			newPosition = encodervalue + 2 * ENC_COUNTS_PER_MICRON;
		} else {
			newPosition = encodervalue - 2 * ENC_COUNTS_PER_MICRON;			
		}

//sprintf(strbuf, "moving to %ld", newPosition);
//printLine(strbuf);

		move_MOTOR(mtraddr, newPosition);
		get_MOTOR_SPEED(mtraddr, &encoderspeed);
		while (encoderspeed) {
			get_MOTOR_SPEED(mtraddr, &encoderspeed);
//sprintf(strbuf, "encoderspeed = %ld", encoderspeed);
//printLine(strbuf);

		}
//		_delay_ms(3000);

		if (get_MOTOR_LIMIT(mtraddr) == NO) {
//sprintf(strbuf, "unstuck at i=%d, opposite direction", i);
//printLine(strbuf);
			stuck = NO;
			break;
		}

		// Try the same direction
		if (direction == MTRDIRNEGATIVE) {
			newPosition = encodervalue - 2 * ENC_COUNTS_PER_MICRON;
		} else {
			newPosition = encodervalue + 2 * ENC_COUNTS_PER_MICRON;
		}
		move_MOTOR(mtraddr, newPosition);
		get_MOTOR_SPEED(mtraddr, &encoderspeed);
		while (encoderspeed) {
			get_MOTOR_SPEED(mtraddr, &encoderspeed);
//sprintf(strbuf, "encoderspeed = %ld", encoderspeed);
//printLine(strbuf);
		}
//		_delay_ms(2000);

		if (get_MOTOR_LIMIT(mtraddr) == NO) {
//sprintf(strbuf, "unstuck at i=%d, same direction", i);
//printLine(strbuf);
			stuck = NO;
			break;
		}
	}
	if (stuck == YES) {		// Tried 3 times and failed
//sprintf(strbuf, "tried 3 times and failed");
//printLine(strbuf);
		return(ERROR);
	}

	// Move 200 um away
	get_MOTOR_ENCODER(mtraddr, &encodervalue);
	if (direction == MTRDIRNEGATIVE) {
		newPosition = encodervalue + 200L * ENC_COUNTS_PER_MICRON;
	} else if (direction == MTRDIRPOSITIVE) {
		newPosition = encodervalue - 200L * ENC_COUNTS_PER_MICRON;
	} 
//sprintf(strbuf, "encodervalue = %ld, newPosition = %ld", encodervalue, newPosition);
//printLine(strbuf);
	move_MOTOR(mtraddr, newPosition);
	return(NOERROR);

}

/*------------------------------------------------------------------------------
void zero_MOTOR_CMD(uint8_t cstack)
	Loads 0 into a motor encoder

	Inputs:
		Command line

	Outputs:
		None
------------------------------------------------------------------------------*/
void zero_MOTOR_CMD(uint8_t cstack)
{

	char strbuf[80];
	const char fmt0[] = "zero_MOTOR_CMD: failed put_MOTOR_ENCODER on %c";
	const char fmt1[] = "zero_MOTOR_CMD: not a motor name (%c)";
	uint8_t motor, mtraddr, retval;

	motor = pcmd[cstack].cobject;	// The char a, b, or c

	switch (motor) {
		case 'a':
		case 'b':
		case 'c':
			mtraddr = motor + 31;
			retval = put_MOTOR_ENCODER(mtraddr, 0L);
			if (retval == ERROR) {
				sprintf(strbuf, fmt0, motor);
				printError(ERR_ZERMTR, strbuf);
				return;
			}
			break;

		default:
			sprintf(strbuf, fmt1, motor);
			printError(ERR_ZERMTR, strbuf);
			break;
		
	}
}
