auomoto/BOSS-specMech/Software/Atmel Studio/2021-12-11 specMech/roboclaw.h

#ifndef ROBOCLAWH
#define ROBOCLAWH

#include "globals.h"

#define ENC_COUNTS_PER_MICRON	283			// 283.1, actually
#define ACCELERATION			7077		// Counts/sec
#define DECELERATION			7077
#define SPEED					7077		// cts/sec
#define MAXCURRENT				(2000)		// mA (Portescap)
//#define MAXCURRENT			(300)		// mA (316.17 mA is absolute max for PI)

#define VOLTS12

#ifdef	VOLTS12
#define PID_P					(72.0)		// Portescap
#define PID_I					(1.0)		// Portescap
#define PID_D					(310.0)		// Portescap
#define PID_MAXI				(144)		// Portescap
#endif

#ifdef	VOLTS24
#define PID_P					(77.0)		// Portescap
#define PID_I					(1.1)		// Portescap
#define PID_D					(330.0)		// Portescap
#define PID_MAXI				(137)		// Portescap
#endif

#define PID_DEADZONE			(6)
#define PID_MINPOS				(-85000)	// Encoder counts (300 um)
#define PID_MAXPOS				(850000)	// 3 mm (894,596 is 3.16 mm)
#define PID_QPPS				(14000)		// Encoder speed at max motor speed
#define S4MODE					(0x42)		// Home(User)/Limit(Fwd)
#define SAVEENCODERFREQUENCY	11			// Save encoder period (sec)
#define ENCODERCOUNT			16
#define ENCODERSPEED			18
#define READFIRMWARE			21
#define PUTENCODER				22
#define READMAINVOLTAGE			24
#define SETQPPS					28			// speed
#define READCURRENT				49
#define READQPPS				55
#define SETPID					61			// Position PID constants
#define READPID					63			// Position PID constants
#define DRIVETO					65			// Buffered drive command
#define SETS4MODE				74
#define GETS4MODE				75
#define READTEMPERATURE			82
#define MOTOR_A					128
#define MOTOR_B					129
#define MOTOR_C					130
#define PUTMAXCURRENT			133
#define GETMAXCURRENT			135

extern volatile uint8_t timerSAVEENCODER;
extern uint8_t timeoutSAVEENCODER;

typedef struct {
	float p, i, d;
	int32_t maxI, deadZone, minPos, maxPos, qpps;
} PID;

uint16_t crc16(uint8_t*, uint16_t);
uint8_t get_FRAM_MOTOR_ENCODER(uint8_t, int32_t*);
uint8_t get_MOTOR(uint8_t, uint8_t, uint8_t*, uint8_t);
uint8_t get_MOTOR_CURRENT(uint8_t, uint16_t*);
uint8_t get_MOTOR_ENCODER(uint8_t, int32_t*);
uint8_t get_MOTOR_FLOAT(uint8_t, uint8_t, float*);
uint8_t get_MOTOR_MAXCURRENT(uint8_t, int32_t*);
uint8_t get_MOTOR_PID(uint8_t, PID*);
uint8_t get_MOTOR_S4MODE(uint8_t, uint8_t*);
uint8_t get_MOTOR_SPEED(uint8_t, int32_t*);
uint8_t init_MOTORS(void);
uint8_t motorsMoving(void);
uint8_t move_MOTOR(uint8_t, int32_t);
uint8_t move_MOTOR_CMD(uint8_t);
uint8_t move_MOTOR_HOME(void);
uint8_t put_FRAM_ENCODERS(void);
uint8_t put_MOTOR(uint8_t, uint8_t, uint8_t*, uint8_t);
uint8_t put_MOTOR_ENCODER(uint8_t, int32_t);
uint8_t put_MOTOR_MAXCURRENT(uint8_t, int32_t);
uint8_t put_MOTOR_PID(uint8_t, PID);
uint8_t put_MOTOR_S4MODE(uint8_t);

#endif
