auomoto/BOSS-specMech/Software/Atmel Studio/specMech/errors.h

#ifndef ERRORSH
#define ERRORSH

#define NOERROR			(0)
#define	ERROR			(99)
#define ERR_GETTIME		(101)	// DS3231 day-time clock not responding
#define ERR_PUTTIME		(102)	// DS3231 day-time clock not responding

#define ERR_BADCOMMAND	(201)	// Command not recognized
#define ERR_BADOBJECT	(302)	// Object not recognized

#define ERR_UNKNOWNMTR	(301)	// Motor not a, b, c, A, B, or C
#define ERR_MOVEREL		(302)	// Relative move, collimator motor
#define ERR_MTRTIMEOUT	(303)	// Roboclaw does not respond to command
#define ERR_MTRREADENC	(304)	// Error reading motor encoder position or speed
#define ERR_MTRENCCRC	(305)	// CRC error from RoboClaw
#define ERR_MTRSETENC	(306)	// Error setting encoder value at initialization
#define ERR_MTRNULLMOVE	(307)	// No distance or target position specified
#define ERR_MOTORMOVING	(308)	// Motor is moving (can't reboot)
#define ERR_MTR_ENC_VAL	(309)	// Invalid motor encoder value
#define ERR_MTR			(310)
#define ERR_ZERMTR		(311)	// Error zeroing motor encoder
#define ERR_TWI			(401)	// start_TWI NACK
#define ERR_MCP23008	(402)	// MCP23008 fail to respond to start condition

#define ERR_FRAM		(403)	// FRAM read/write error

#define ERR_PNUMECH		(501)	// Not a valid mechanism (s, l, r, or b)
#define ERR_SET			(601)	// Bad object to set
#define ERR_SETTIME		(602)	// Invalid time format
#define ERR_ISO			(603)	// ISOTIME error

#define ERR_FAN			(700)	// Fan command error (not + or -)

#define ERR_LN2			(800)	// LN2 communications error

extern volatile uint8_t squelchErrors;
void printError(uint16_t, char*);

#endif
