auomoto/BOSS-specMech/Software/Atmel Studio/specMech/globals.h

#ifndef GLOBALSH
#define GLOBALSH

//#define VERBOSE

//#define F_CPU		3333333UL
#define F_CPU		10000000UL
#define VERSION		"2022-06-20"
#define	YES			1
#define	NO			0
#define ON			1
#define OFF			0
#define BADFLOAT	(-666.0)
#define BADINT		(0xFFFF);
#define BADLONG		(0xFFFFFFFF)

// Port macros
#define get_SPECID		(PORTF.IN & PIN2_bm ? 2 : 1)
#define off_LED			(PORTF.OUTSET = PIN5_bm)
#define on_LED			(PORTF.OUTCLR = PIN5_bm)
#define toggle_LED		(PORTF.OUTTGL = PIN5_bm)
#define off_BEEPER		(PORTB.OUTCLR = PIN2_bm)
#define on_BEEPER		(PORTB.OUTSET = PIN2_bm)
#define toggle_BEEPER	(PORTB.OUTTGL = PIN2_bm)

#include <avr/io.h>
#include <util/delay.h>
#include <avr/interrupt.h>
#include <stdio.h>		// sprintf
#include <stdlib.h>		// atol()
#include <string.h>		// for strcpy, strlen

#endif
