auomoto/BOSS-specMech/Software/Atmel Studio/specMech/initialize.h

#ifndef INITIALIZEH
#define INITIALIZEH

#include "oled.h"
#include "eeprom.h"
#include "roboclaw.h"
#include "timers.h"
#include "psvoltage.h"
#include "beeper.h"

//void init_BEEPER(void);
void init_EEPROM(void);
void init_LED(void);
uint8_t init_MMA8451(void);
void init_OLED(void);
uint8_t init_PNEU(void);
void init_PORTS(void);
void init_RTC(uint16_t);
void init_SPECID(void);
void init_TWI(void);
void init_XPORT(void);
void init_USART(void);
void initialize(void);

extern uint8_t rebootackd;

#endif
