auomoto/BOSS-specMech/Software/Atmel Studio/2021-12-11 specMech/errors.c

#include "globals.h"
#include "usart.h"
#include "commands.h"
#include "nmea.h"
#include "errors.h"

volatile uint8_t squelchErrors;

/*------------------------------------------------------------------------------
void printError(uint8_t errorNumber, char *errorString)
	Prints an error report on USART0
------------------------------------------------------------------------------*/
void printError(uint16_t errorNumber, char *errorString)
{

	char strbuf[BUFSIZE];
	const char errorFormat[] = "ERR,%d,%s";

squelchErrors=NO;
	if (!squelchErrors) {
		sprintf(strbuf, errorFormat, errorNumber, errorString);
		printLine(strbuf);
	}

}
